rothmanhunterd/VoronX/hardware/CAD_files/STLs/Print_Head_Cable_Chain.STL

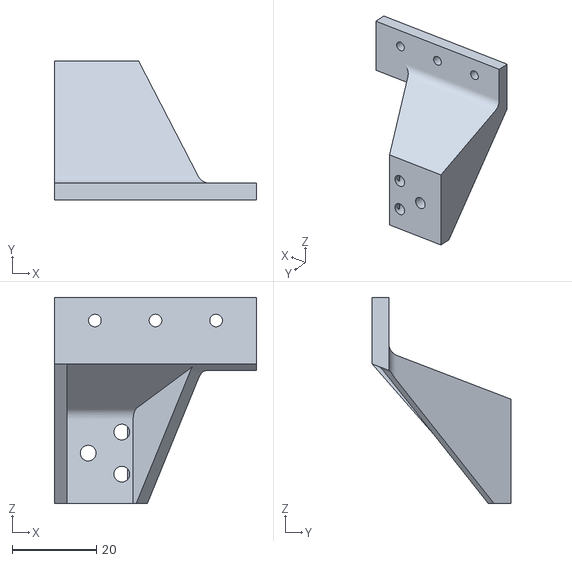
[picture p15: CAD file, 2024-08-09]
hardware/CAD_files/STLs/Print_Head_Cable_Chain.STL
48.0 x 33.0 x 49.0
