rothmanhunterd/VoronX/hardware/CAD_files/STLs/XY_Connector.STL

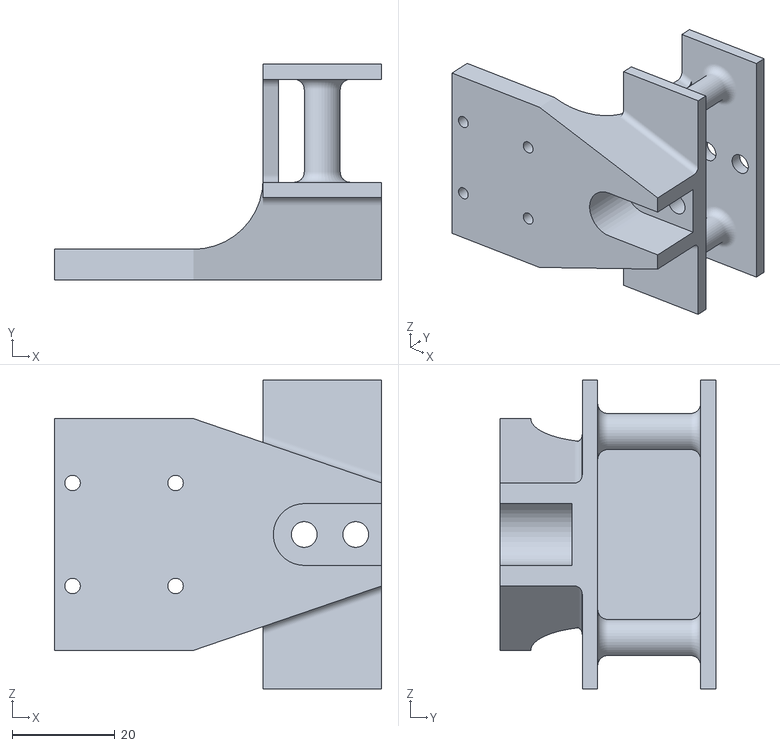
[picture p16: CAD file, 2024-08-09]
hardware/CAD_files/STLs/XY_Connector.STL
63.5 x 42.0 x 60.0
