rothmanhunterd/VoronX/hardware/CAD_files/STLs/Foot_Pad.STL

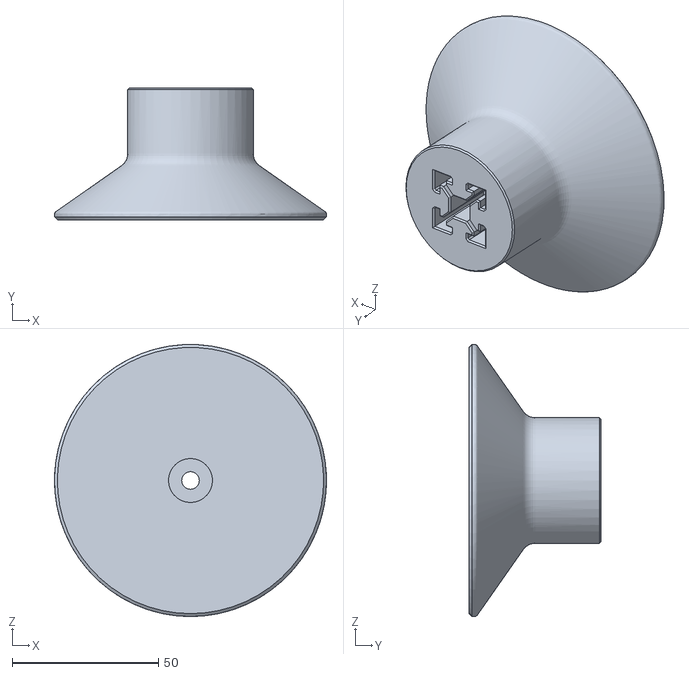
[picture p17: CAD file, 2024-08-09]
hardware/CAD_files/STLs/Foot_Pad.STL
92.8 x 45.0 x 92.9
