rothmanhunterd/VoronX/hardware/CAD_files/STLs/XY_Cable_Chain_Mount_Right.STL

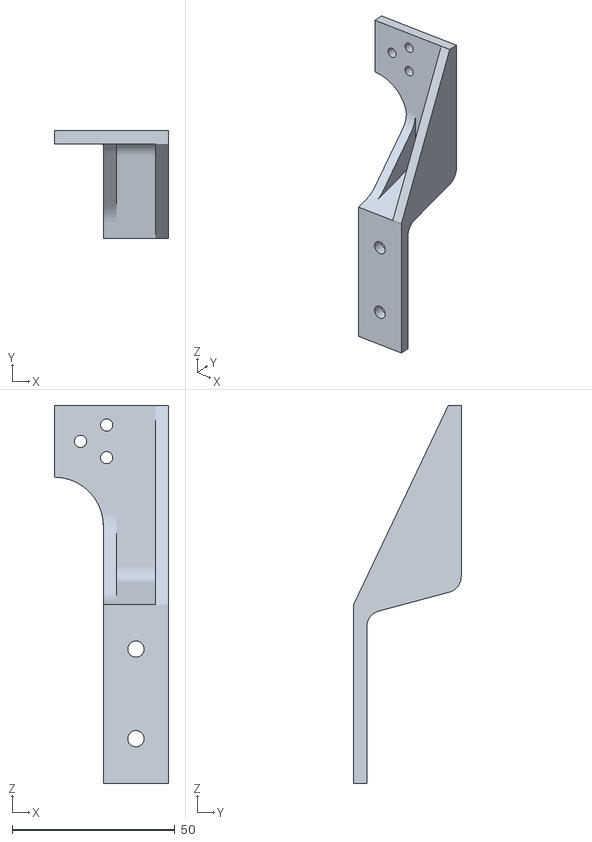
[picture p18: CAD file, 2024-08-09]
hardware/CAD_files/STLs/XY_Cable_Chain_Mount_Right.STL
35.0 x 33.0 x 116.0
