rothmanhunterd/VoronX/hardware/CAD_files/STLs/Bearing_Bracket.STL

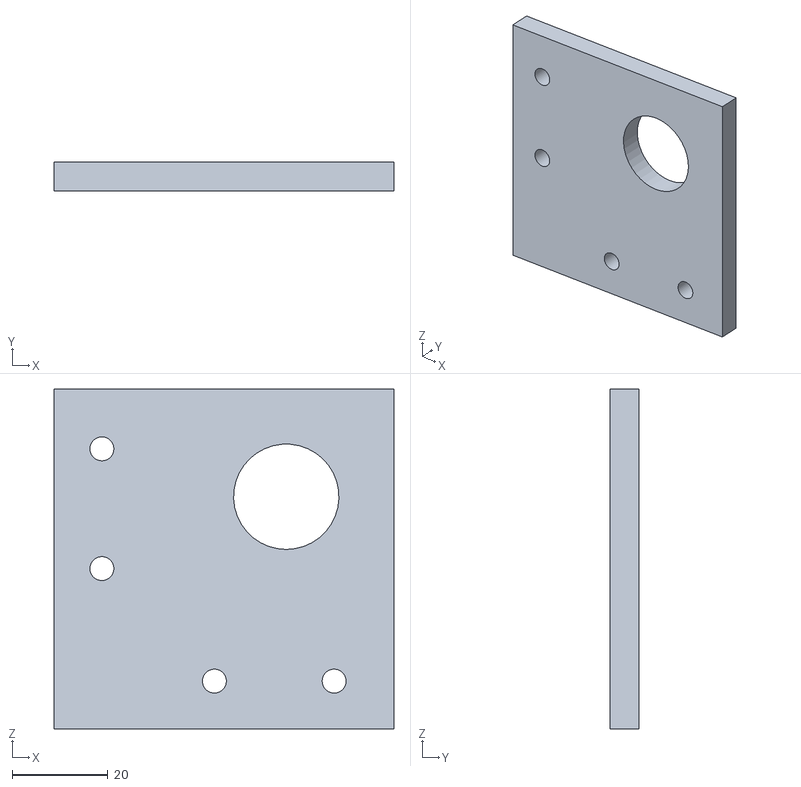
[picture p19: CAD file, 2024-08-09]
hardware/CAD_files/STLs/Bearing_Bracket.STL
71.0 x 6.00 x 71.0
