rothmanhunterd/VoronX/hardware/CAD_files/STLs/Limit_Switch_Mounts.STL

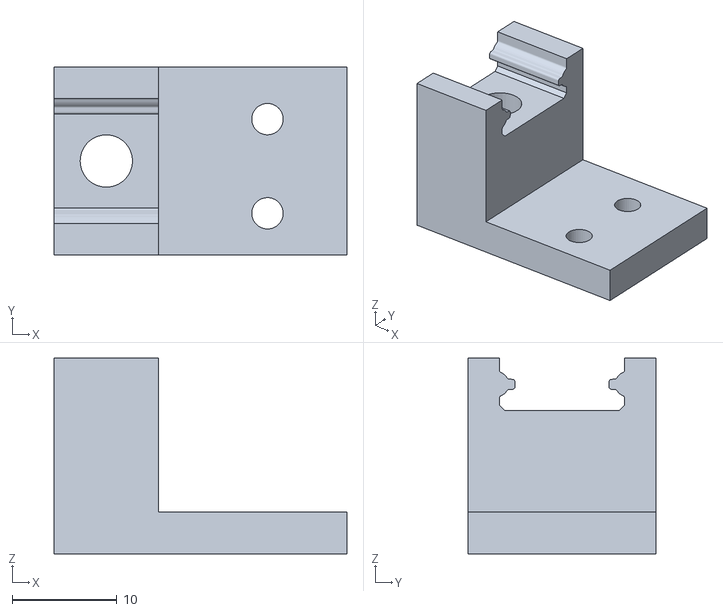
[picture p20: CAD file, 2024-08-09]
hardware/CAD_files/STLs/Limit_Switch_Mounts.STL
28.0 x 18.0 x 18.7
