rothmanhunterd/VoronX/hardware/CAD_files/STLs/Filament_Sensor_Bottom.STL

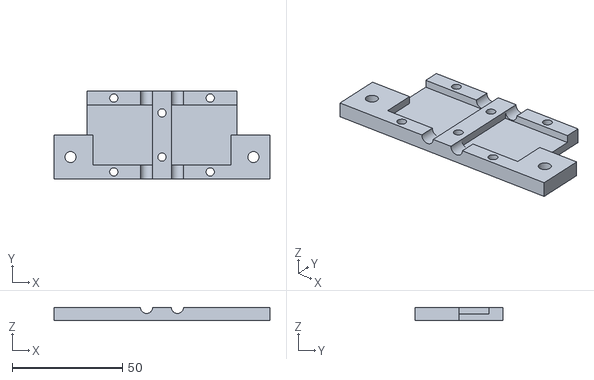
[picture p21: CAD file, 2024-08-09]
hardware/CAD_files/STLs/Filament_Sensor_Bottom.STL
98.0 x 40.0 x 6.00
