rothmanhunterd/VoronX/hardware/CAD_files/STLs/Power_Switch_Mount.STL

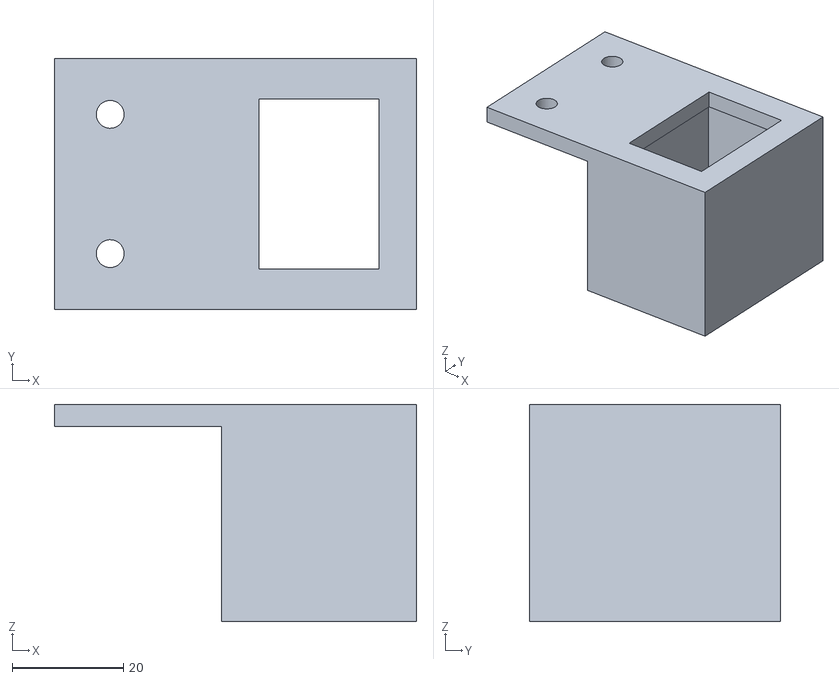
[picture p22: CAD file, 2024-08-09]
hardware/CAD_files/STLs/Power_Switch_Mount.STL
65.0 x 45.0 x 39.0
