rothmanhunterd/VoronX/hardware/CAD_files/STLs/Z_Axis_Cable_Chain_Mount.STL

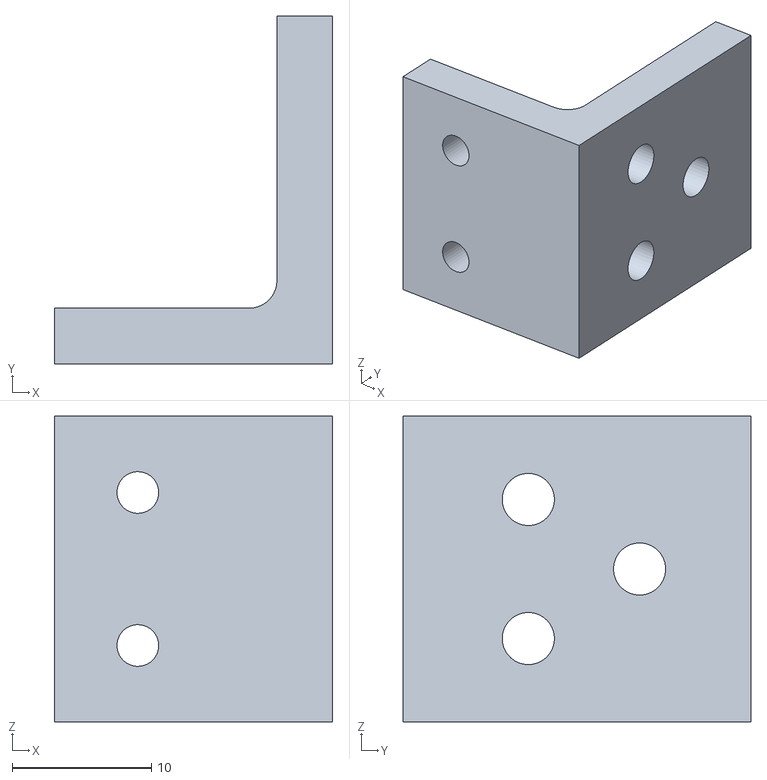
[picture p23: CAD file, 2024-08-09]
hardware/CAD_files/STLs/Z_Axis_Cable_Chain_Mount.STL
20.0 x 25.0 x 22.0
