rothmanhunterd/VoronX/hardware/CAD_files/STLs/Gantry_Linear_Rail_Connector_Back.STL

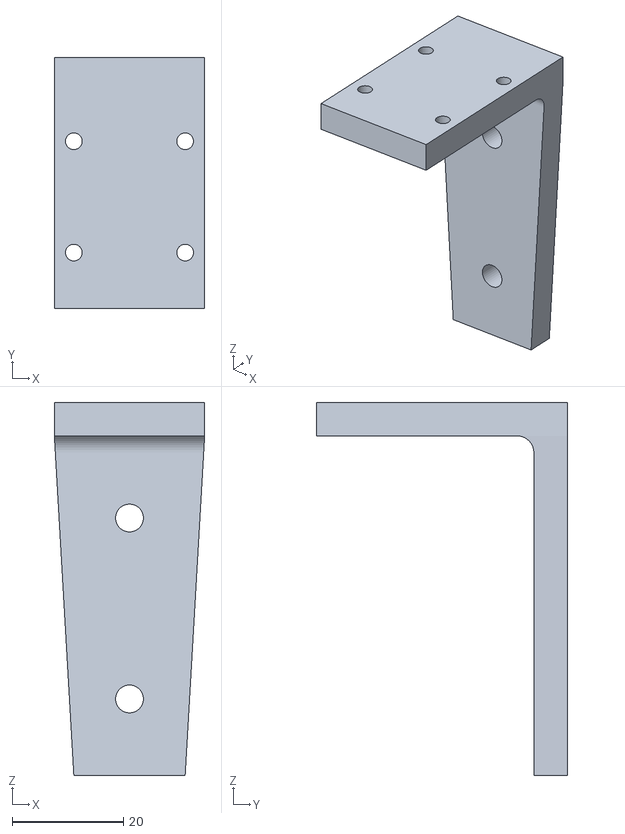
[picture p24: CAD file, 2024-08-09]
hardware/CAD_files/STLs/Gantry_Linear_Rail_Connector_Back.STL
27.0 x 45.0 x 67.0
