rothmanhunterd/VoronX/hardware/CAD_files/Drawings/Y_Stepper_Drive_Motor_Plate.pdf

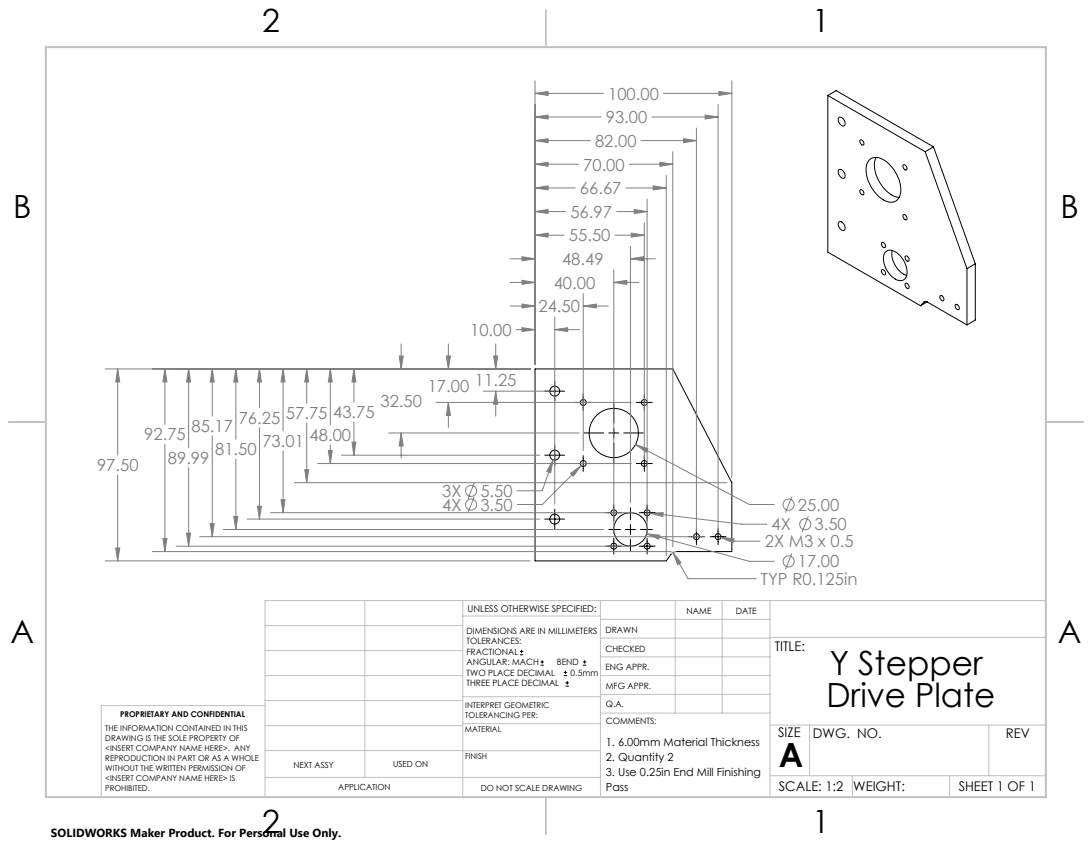
[picture p26: page 1]
TYP R0.125in

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

CHECKED | | | TITLE: Y Stepper Drive Plate

ENG APPR.
MFG APPR.

INTERPRET GEOMETRIC TOLERANCING PER: | Q.A.
MATERIAL | | SIZE A | DWG. NO. | REV

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

COMMENTS:
1. 6.00mm Material Thickness
2. Quantity 2
3. Use 0.25in End Mill Finishing
Pass

NEXT ASSY | USED ON | FINISH

APPLICATION | DO NOT SCALE DRAWING | | SCALE: 1:2 | WEIGHT: | SHEET 1 OF 1

SOLIDWORKS Maker Product. For Personal Use Only.
