rothmanhunterd/VoronX/hardware/CAD_files/Drawings/Z_Stepper_Motor_Plate.pdf

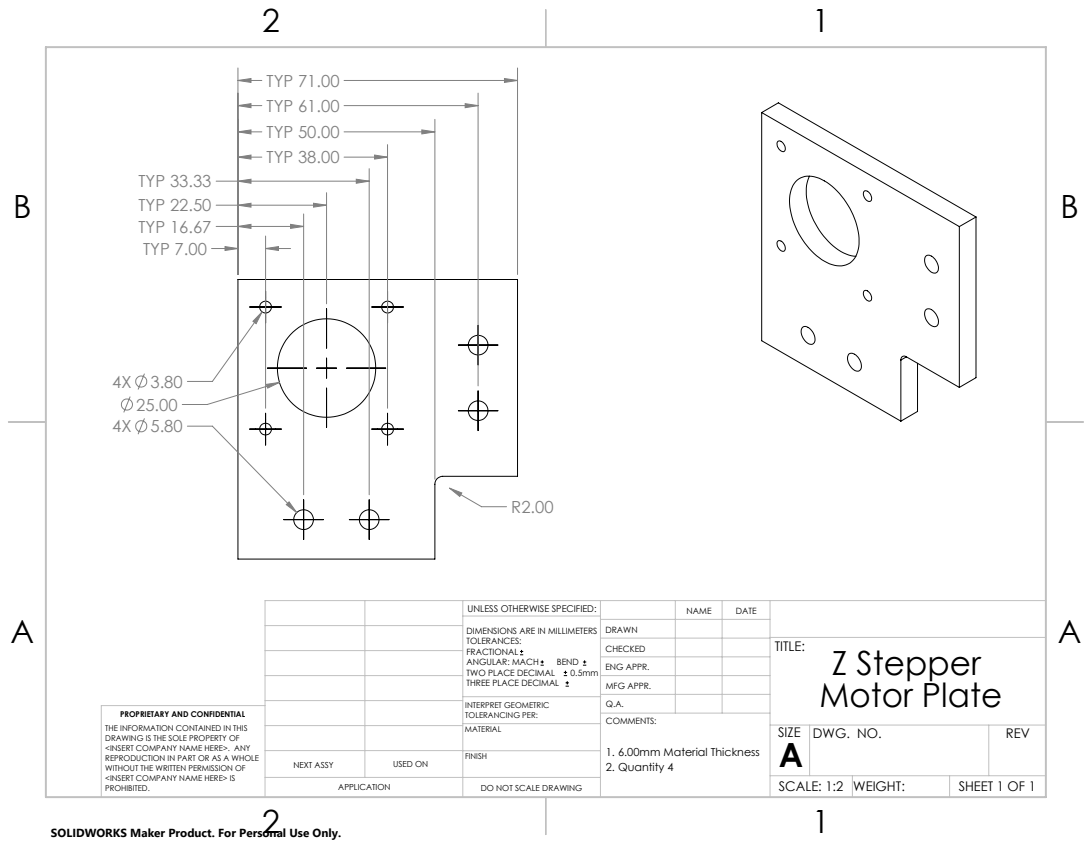
[picture p27: page 1]
TYP 71.00; TYP 50.00; TYP 16.67; TYP 33.33 TYP 22.50; TYP 7.00; TYP 38.00; TYP 61.00; 1. 6.00mm Material Thickness 2. Quantity 4

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

CHECKED | | | TITLE: Z Stepper Motor Plate

ENG APPR.
MFG APPR.

INTERPRET GEOMETRIC TOLERANCING PER: | Q.A.
MATERIAL | | SIZE A | DWG. NO. | REV

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

NEXT ASSY | USED ON | FINISH

APPLICATION | DO NOT SCALE DRAWING | | SCALE: 1:2 | WEIGHT: | SHEET 1 OF 1

SOLIDWORKS Maker Product. For Personal Use Only.
