rothmanhunterd/VoronX/firmware/config/adxl.cfg

[mcu btt_adxl345]
serial: /dev/serial/by-id/usb-Klipper_rp2040_454741505B0719DA-if00

[adxl345]
cs_pin: btt_adxl345:gpio9
spi_software_sclk_pin: btt_adxl345:gpio10
spi_software_mosi_pin: btt_adxl345:gpio11
spi_software_miso_pin: btt_adxl345:gpio8
axes_map: y,-x,z

[resonance_tester]
probe_points: 234, 330, 300
accel_chip: adxl345
